codepainters/e800j_grafix/img/screen_2_bad.jpg

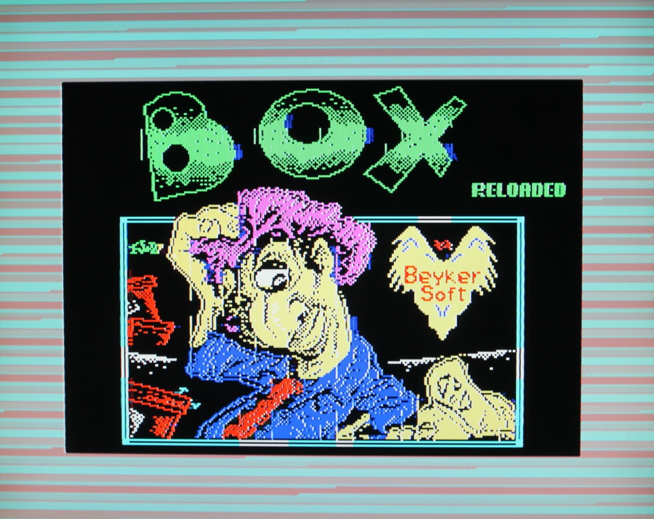
img/screen_2_bad.jpg
