codepainters/e800j_grafix/img/screen_3_bad.jpg

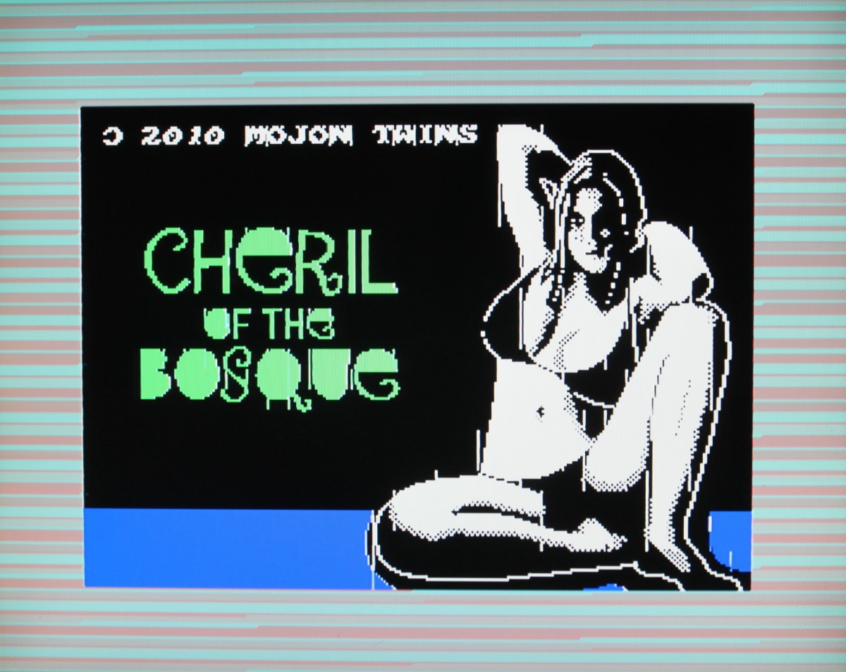
img/screen_3_bad.jpg
